3ym3ym/fT_jig/ft_jig.kicad_sch

## KiCad design ft_jig.kicad_sch (2025-05-03)

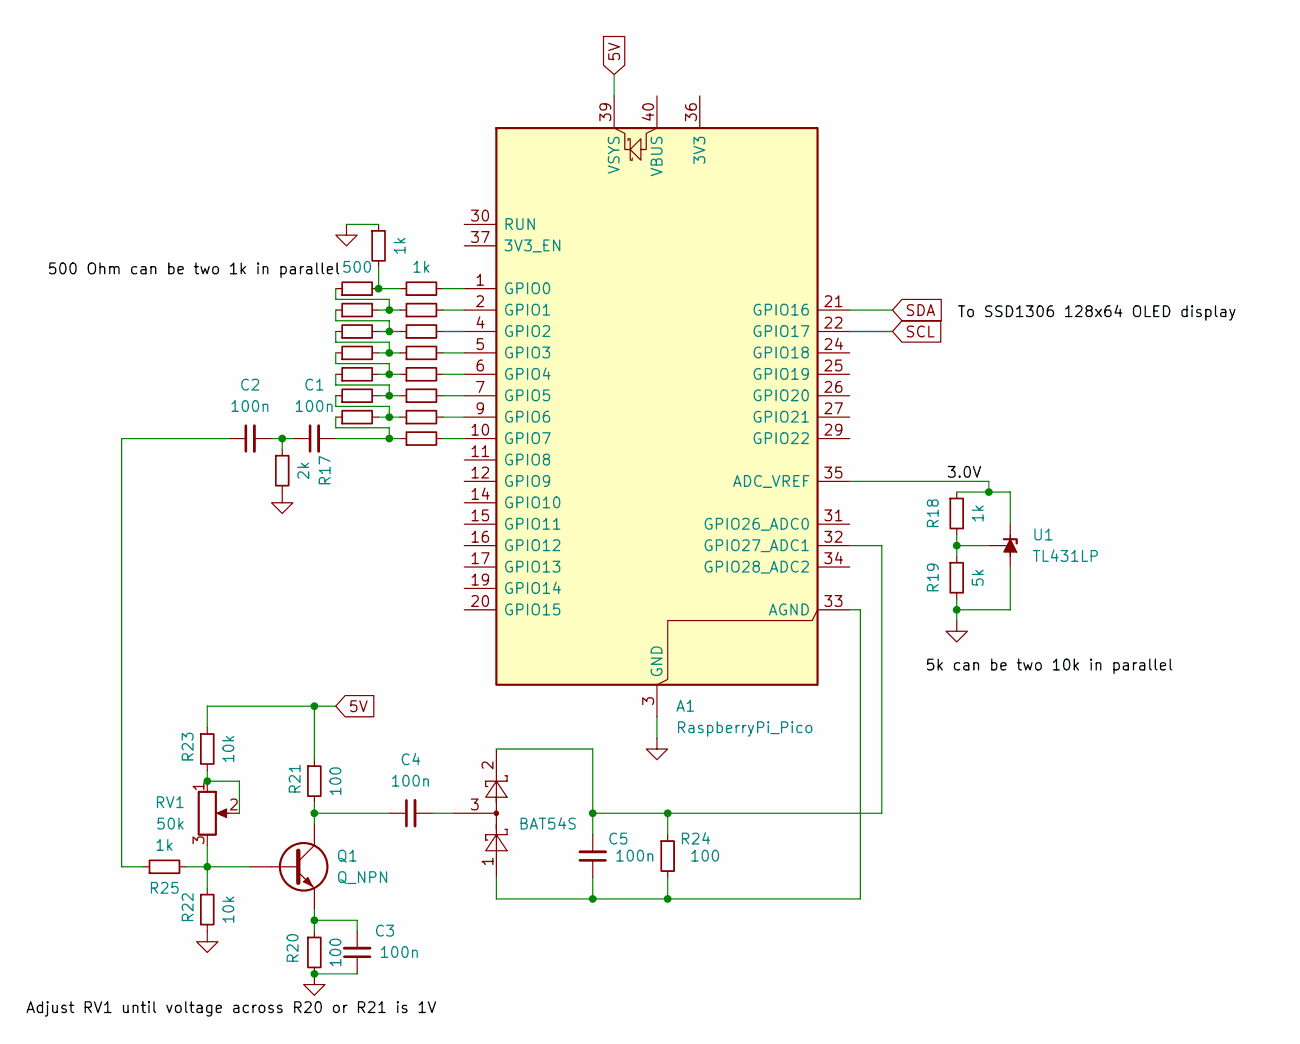
[picture p2: schematic ft_jig.kicad_sch]

Parts:
A1: RaspberryPi_Pico; RaspberryPi_Pico_Common_Unspecified
C1, C2, C3, C4, C5: 100n
D1: BAT54S; SOT-23
Q1: Q_NPN
R1, R2, R3, R4, R5, R6, R7, R8, R9, R11, R12, R13, R14, R15, R16, R18, R25: 1k
R10: 500
R17: 2k
R19: 5k
R20, R21, R24: 100
R22, R23: 10k
RV1: 50k
U1: TL431LP; TO-92_Inline

Connections:
3.0V: A1.35 (ADC_VREF), R18.1, U1.3 (K)
5V: A1.39 (VSYS), R21.1, R23.1
GND: A1.3 (GND), A1.8 (GND), A1.13 (GND), A1.18 (GND), A1.23 (GND), A1.28 (GND), A1.38 (GND), C3.1, R1.1, R17.2, R19.2, R20.2, R22.2, U1.2 (A)
unnamed: A1.1 (GPIO0), R2.2
unnamed: A1.2 (GPIO1), R3.2
unnamed: A1.4 (GPIO2), R4.2
unnamed: A1.5 (GPIO3), R5.2
unnamed: A1.6 (GPIO4), R6.2
unnamed: A1.7 (GPIO5), R7.2
unnamed: A1.9 (GPIO6), R8.2
unnamed: A1.10 (GPIO7), R9.2
unnamed: A1.32 (GPIO27_ADC1), C5.2, D1.2 (K), R24.1
unnamed: A1.33 (AGND), C5.1, D1.1 (A), R24.2
unnamed: C1.1, C2.2, R17.1
unnamed: C1.2, R9.1, R16.1
unnamed: C2.1, R25.1
unnamed: C3.2, Q1.E, R20.1
unnamed: C4.1, Q1.C, R21.2
unnamed: C4.2, D1.3 (COM)
unnamed: Q1.B, R22.1, R25.2, RV1.3
unnamed: R1.2, R2.1, R10.2
unnamed: R3.1, R10.1, R11.2
unnamed: R4.1, R11.1, R12.2
unnamed: R5.1, R12.1, R13.2
unnamed: R6.1, R13.1, R14.2
unnamed: R7.1, R14.1, R15.2
unnamed: R8.1, R15.1, R16.2
unnamed: R18.2, R19.1, U1.1 (REF)
unnamed: R23.2, RV1.1, RV1.2
SCL: A1.22 (GPIO17)
SDA: A1.21 (GPIO16)
